velumanohar2000/IEEE-R5-Robotics-2024/Software/Testing/motor_calibration/src/main.cpp

#include <Arduino.h>
#include <stdbool.h>
#include <Adafruit_BNO08x.h>
#include <Wire.h>
#include <math.h>
#include <ESP32MotorControl.h>
#include <LiquidCrystal_I2C.h>
#include <string.h>

#include "BNO085_heading_acceleration.h"
#include "motor_control_v2.h"
//#include "printToLcd.h"

// #define CALIBRATE_STRAIGHT_LINE
//  #define TEST_TURNS

// After starting/resetting the robot you have 5 seconds to align it with 0 degress
// We need to implement a blovking function that waits unitl button pressed before locking in 0
// Also we need to implement a lcd screen to show us our angle without uart

/*
 * Global Variables for LCD Display
 */
LiquidCrystal_I2C lcd(0x27, 16, 2); // set the LCD address to 0x27 for a 16 chars and 2 line display
char lcdStr[16];
/*
 *Global Variable for the Motors
 */
ESP32MotorControl motors;
// LEFT MOTOR
const uint8_t MOTOR_A_IN_1 = 5;
const uint8_t MOTOR_A_IN_2 = 4;
int16_t A_LEFT_MOTOR_OFFSET = 0;

// RIGHT MOTOR
const uint8_t MOTOR_B_IN_3 = 7;
const uint8_t MOTOR_B_IN_4 = 6;
int16_t B_RIGHT_MOTOR_OFFSET = 2;

/*
 * Global Variable for IMU
 */
Adafruit_BNO08x bno08x;
sh2_SensorValue_t sensorValue;
float offset = 0;

// float getHeading()
// {

//   float retVal = -1;

//   if (bno08x.getSensorEvent(&sensorValue))
//   {
//     retVal = calculateHeading(sensorValue.un.arvrStabilizedRV.i, sensorValue.un.arvrStabilizedRV.j, sensorValue.un.arvrStabilizedRV.k, sensorValue.un.arvrStabilizedRV.real);

//     retVal -= offset;
//     if (retVal < 0)
//     {
//       retVal += 359.99;
//     }
//   }

//   return retVal;
// }
// float getCurrentAngle()
// {
//   float currentAngle = -1;
//   while (currentAngle == -1)
//   {
//     currentAngle = getHeading();
//   }
//   return currentAngle;
// }
// void printCurrentAngle()
// {
//   float currentAngle = getCurrentAngle();
//   printToLcd("Current Angle: ", currentAngle);
// }

// void turnToHeading(float goal, uint8_t speed)
// {
//   float absVal;
//   float angleDiff;
//   uint8_t i = 0;

//   float currentAngle = getCurrentAngle();

//   printToLcd("Current Angle: ", currentAngle);
//   angleDiff = goal - currentAngle;
//   absVal = abs(angleDiff);
//   if (absVal > 350)
//   {
//     absVal = 359.99 - absVal;
//     angleDiff = 359.99 - angleDiff;
//   }
//   Serial.println(angleDiff);
//   Serial.println(absVal);
//   Serial.println();

//   while (absVal > 10)
//   {
//     // Serial.print("abs: ");
//     // Serial.print(absVal);
//     // Serial.print(" angle: ");
//     // Serial.print(currentAngle);

//     if ((angleDiff >= 0) && (absVal <= 180))
//     {
//       // Serial.print(" case 1: ");
//       turn(COUNTER_CLOCKWISE, speed);
//     }
//     else if ((angleDiff < 0) && (absVal <= 180))
//     {
//       // Serial.print(" case 2: ");
//       turn(CLOCKWISE, speed);
//     }
//     else if ((angleDiff >= 0) && (absVal >= 180))
//     {
//       // Serial.print(" case 3: ");
//       turn(CLOCKWISE, speed);
//     }
//     else
//     {
//       // Serial.print(" case 4: ");
//       turn(COUNTER_CLOCKWISE, speed);
//     }

//     currentAngle = getCurrentAngle();
//     i++;
//     if (i >= 30)
//     {
//       printCurrentAngle();
//       i = 0;
//     }

//     // Serial.println(goal);
//     angleDiff = goal - currentAngle;
//     absVal = abs(angleDiff);
//     if (absVal > 350)
//     {
//       absVal = 359.99 - absVal;
//       angleDiff = 359.99 - angleDiff;
//     }
//     Serial.println(angleDiff);
//     Serial.println(absVal);
//     Serial.println();
//   }
//   stop();
// }

void testTurns()
{
  turnToHeading(90, 85);
  /// printCurrentAngle();
  delay(1000);

  turnToHeading(0, 85);
  // printCurrentAngle();
  delay(1000);

  turnToHeading(180, 85);
  // printCurrentAngle();
  delay(1000);

  turnToHeading(0, 85);
  // printCurrentAngle();
  delay(1000);

  turnToHeading(270, 85);
  // printCurrentAngle();
  delay(1000);

  turnToHeading(45, 85);
  // printCurrentAngle();
  delay(1000);

  turnToHeading(225, 85);
  // printCurrentAngle();
  delay(1000);

  turnToHeading(135, 85);
  // printCurrentAngle();
  delay(1000);

  turnToHeading(315, 85);
  // printCurrentAngle();
  delay(1000);
}

void setup()
{
  Serial.begin(115200);
  Wire.begin(9, 8);

  lcd.init(); // initialize the lcd
  lcd.backlight();

  setupBNO085(&bno08x);
  motors.attachMotors(MOTOR_A_IN_1, MOTOR_A_IN_2, MOTOR_B_IN_3, MOTOR_B_IN_4);
  float currentAngle;
  uint8_t i = 0;
  Serial.println("*****TEST HEADING******\n\n");

  // printToLcd("HEADING", "TEST");
  delay(1000);
  // printToLcd("Position to 0", "degrees");

  for (i = 3; i > 0; i--)
  {
    //   printToLcd("Time left: ", i);
    delay(1000);
  }

  offset = getCurrentAngle();

  Serial.println("offset: ");
  Serial.println(offset);

  currentAngle = getCurrentAngle();

  Serial.print("Current Angle: ");
  Serial.println(currentAngle);

 // printToLcd("OFFSET:", offset);
  delay(1000);
  // printCurrentAngle();
  delay(1000);
}
// void driveToHeading(float goalHeading)
// {
//   float currentAngle = -1;
//   float absVal;
//   float angleDiff;
//   unsigned long currentMillis;
//   unsigned long previousMillis = 0;
//   uint32_t interval = 1000;
//   uint16_t i = 0;

//   bool goToHeading = true;
//   while (goToHeading)
//   {
//     currentAngle = getCurrentAngle();

//     i++;
//     if (i == 30)
//     {
//       printToLcd("Current Angle: ", currentAngle);
//       i = 0;
//     }
//     angleDiff = goalHeading - currentAngle;
//     absVal = abs(angleDiff);
//     // Serial.println(absVal);
//     if (absVal > 345)
//     {
//       absVal = 359.99 - absVal;
//       angleDiff = 359.99 - angleDiff;
//     }
//     Serial.println(angleDiff);
//     Serial.println(absVal);
//     Serial.println();

//     if (absVal > 15)
//     {
//       turnToHeading(goalHeading, 65);
//       previousMillis = currentMillis = millis();
//     }
//     else if (absVal <= 15 && absVal >= 3)
//     {
//       if ((angleDiff >= 0) && (absVal <= 180))
//       {
//         // Serial.print(" case 1: ");
//         turn2(COUNTER_CLOCKWISE, 65, 30);
//       }
//       else if ((angleDiff < 0) && (absVal <= 180))
//       {
//         // Serial.print(" case 2: ");
//         turn2(CLOCKWISE, 65, 30);
//       }
//       else if ((angleDiff >= 0) && (absVal >= 180))
//       {
//         // Serial.print(" case 3: ");
//         turn2(CLOCKWISE, 65, 30);
//       }
//       else
//       {
//         // Serial.print(" case 4: ");
//         turn2(COUNTER_CLOCKWISE, 65, 30);
//       }
//       previousMillis = currentMillis = millis();
//     }
//     else if (absVal < 5 && absVal >= 2)
//     {
//       if ((angleDiff >= 0) && (absVal <= 180))
//       {
//         // Serial.print(" case 1: ");
//         turn2(COUNTER_CLOCKWISE, 65, 10);
//       }
//       else if ((angleDiff < 0) && (absVal <= 180))
//       {
//         // Serial.print(" case 2: ");
//         turn2(CLOCKWISE, 65, 10);
//       }
//       else if ((angleDiff >= 0) && (absVal >= 180))
//       {
//         // Serial.print(" case 3: ");
//         turn2(CLOCKWISE, 65, 10);
//       }
//       else
//       {
//         // Serial.print(" case 4: ");
//         turn2(COUNTER_CLOCKWISE, 65, 10);
//       }
//       unsigned long currentMillis = millis();

//       if (currentMillis - previousMillis >= interval)
//       {
//         previousMillis = currentMillis;
//         if (previousMillis != 0)
//         {
//           goToHeading = false;
//           stop();
//         }
//       }
//     }
//     else
//     {
//       move(FORWARD, 65);

//       if (currentMillis - previousMillis >= interval)
//       {
//         previousMillis = currentMillis;
//         if (previousMillis != 0)
//         {
//           goToHeading = false;
//           stop();
//         }
//       }
//     }
//   }
// }

void calibrateStraightLine()
{
  move(FORWARD, 75);
  delay(4000);
  stop();
  move(BACKWARD, 75);
  delay(4000);
  stop();
}

unsigned long currentMillis = 0;
unsigned long previousMillis = 0; // will store last time LED was updated

void loop()
{
#ifdef CALIBRATE_STRAIGHT_LINE
  calibrateStraightLine(); // change, left and right motor offset untill car goes straight for 4 seconds
  while (1)
    ;
#endif
#ifdef TEST_TURNS
  turn(COUNTER_CLOCKWISE);
  delay(2000);
  turn(CLOCKWISE);
  delay(2000);
  stop();
  delay(2000);
  testTurns(); // fix turning speed until angle is within desired range of goal heading
#endif
  previousMillis = currentMillis = millis();
  while (currentMillis - previousMillis < 1000)
  {
    driveToHeading(270);
    currentMillis = millis();
  }
  stop();
  delay(1000);
  previousMillis = currentMillis = millis();

  while (currentMillis - previousMillis < 1000)
  {
    driveToHeading(0);
    currentMillis = millis();
  }
  stop();
  delay(1000);
  previousMillis = currentMillis = millis();

  while (currentMillis - previousMillis < 1000)
  {
    driveToHeading(90);
    currentMillis = millis();
  }
  stop();
  delay(1000);
  previousMillis = currentMillis = millis();

  while (currentMillis - previousMillis < 1000)
  {
    driveToHeading(180);
    currentMillis = millis();
  }
  stop();
  delay(1000);
}
