velumanohar2000/IEEE-R5-Robotics-2024/Software/Testing/front_lidar_test_VL53L4CX/src/main.cpp

/**
 ******************************************************************************
 * @file    VL53L4CX_Sat_HelloWorld_Interrupt.ino
 * @author  SRA
 * @version V1.0.0
 * @date    16 March 2022
 * @brief   Arduino test application for the STMicrolectronics VL53L4CX
 *          proximity sensor satellite based on FlightSense.
 *          This application makes use of C++ classes obtained from the C
 *          components' drivers.
 ******************************************************************************
 * @attention
 *
 * <h2><center>&copy; COPYRIGHT(c) 2022 STMicroelectronics</center></h2>
 *
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
 ******************************************************************************
 */

//On some boards like the Arduino Uno the pin used by the sensor to raise interrupts (A2)
//can't be mapped as an interrupt pin. For this this reason this sketch will not work
//unless some additional cabling is done and the interrupt pin is changed.
/*
 * To use this sketch you need to connect the VL53L4CD satellite sensor directly to the Nucleo board with wires in this way:
 * pin 1 (GND) of the VL53L4CD satellite connected to GND of the Nucleo board
 * pin 2 (VDD) of the VL53L4CD satellite connected to 3V3 pin of the Nucleo board
 * pin 3 (SCL) of the VL53L4CD satellite connected to pin D15 (SCL) of the Nucleo board
 * pin 4 (SDA) of the VL53L4CD satellite connected to pin D14 (SDA) of the Nucleo board
 * pin 5 (GPIO1) of the VL53L4CD satellite connected to pin A2 of the Nucleo board
 * pin 6 (XSHUT) of the VL53L4CD satellite connected to pin A1 of the Nucleo board
 */
/* Includes ------------------------------------------------------------------*/
#include <Arduino.h>
#include <Wire.h>
#include <vl53l4cx_class.h>
#include <string.h>
#include <stdlib.h>
#include <stdio.h>
#include <stdint.h>
#include <assert.h>
#include <stdlib.h>

#define DEV_I2C Wire
#define SerialPort Serial

#ifndef LED_BUILTIN
  #define LED_BUILTIN 13
#endif
#define LedPin LED_BUILTIN

#define interruptPin A2

// Components.
VL53L4CX sensor_vl53l4cx_sat(&DEV_I2C, A1);

volatile int interruptCount = 0;

void measure()
{
  interruptCount = 1;
}

void setup()
{
  VL53L4CX_Error status;
  // Led.
  pinMode(LedPin, OUTPUT);
  pinMode(interruptPin, INPUT_PULLUP);
  attachInterrupt(interruptPin, measure, FALLING);

  // Initialize serial for output.
  SerialPort.begin(115200);
  SerialPort.println("Starting...");

  // Initialize I2C bus.
  DEV_I2C.begin(9,8);

  // Configure VL53L4CX satellite component.
  sensor_vl53l4cx_sat.begin();

  // Switch off VL53L4CX satellite component.
  sensor_vl53l4cx_sat.VL53L4CX_Off();

  // Initialize VL53L4CX satellite component.
  status = sensor_vl53l4cx_sat.InitSensor(0x12);
  if (status) {
    SerialPort.println("Init sensor_vl53l4cx_sat failed...");
  }

  sensor_vl53l4cx_sat.VL53L4CX_StartMeasurement();
}

void loop()
{
  VL53L4CX_MultiRangingData_t MultiRangingData;
  VL53L4CX_MultiRangingData_t *pMultiRangingData = &MultiRangingData;
  uint8_t NewDataReady = 0;
  int no_of_object_found = 0, j;
  char report[64];
  if (interruptCount) {
    int status;

    interruptCount = 0;
    // Led blinking.
    digitalWrite(LedPin, HIGH);

    status = sensor_vl53l4cx_sat.VL53L4CX_GetMeasurementDataReady(&NewDataReady);
    if ((!status) && (NewDataReady != 0)) {
      status = sensor_vl53l4cx_sat.VL53L4CX_GetMultiRangingData(pMultiRangingData);
      no_of_object_found = pMultiRangingData->NumberOfObjectsFound;
      snprintf(report, sizeof(report), "Count=%d, #Objs=%1d ", pMultiRangingData->StreamCount, no_of_object_found);
      SerialPort.print(report);
      for (j = 0; j < no_of_object_found; j++) {
        if (j != 0) {
          SerialPort.print("\r\n                   ");
        }
        SerialPort.print("status=");
        SerialPort.print(pMultiRangingData->RangeData[j].RangeStatus);
        SerialPort.print(", D=");
        SerialPort.print(pMultiRangingData->RangeData[j].RangeMilliMeter);
        SerialPort.print("mm");
        SerialPort.print(", Signal=");
        SerialPort.print((float)pMultiRangingData->RangeData[j].SignalRateRtnMegaCps / 65536.0);
        SerialPort.print(" Mcps, Ambient=");
        SerialPort.print((float)pMultiRangingData->RangeData[j].AmbientRateRtnMegaCps / 65536.0);
        SerialPort.print(" Mcps");
      }
      SerialPort.println("");
      if (status == 0) {
        status = sensor_vl53l4cx_sat.VL53L4CX_ClearInterruptAndStartMeasurement();
      }
    }

    digitalWrite(LedPin, LOW);
  }
}
