velumanohar2000/IEEE-R5-Robotics-2024/Software/Testing/VL53L5CX_test/src/main.cpp

/*
  Read an 8x8 array of distances from the VL53L5CX
  By: Nathan Seidle
  SparkFun Electronics
  Date: October 26, 2021
  License: MIT. See license file for more information but you can
  basically do whatever you want with this code.

  This example shows how to read all 64 distance readings at once.

  Feel like supporting our work? Buy a board from SparkFun!
  https://www.sparkfun.com/products/18642

*/
#include <Arduino.h>

#include <Wire.h>

#include <SparkFun_VL53L5CX_Library.h> //http://librarymanager/All#SparkFun_VL53L5CX

SparkFun_VL53L5CX myImager;
VL53L5CX_ResultsData measurementData; // Result data class structure, 1356 byes of RAM

int imageResolution = 0; //Used to pretty print output
int imageWidth = 0; //Used to pretty print output

int imageArray[16];

void setup()
{
  Serial.begin(115200);
  delay(1000);
  Serial.println("SparkFun VL53L5CX Imager Example");

  Wire.begin(9, 8); //This resets to 100kHz I2C
  Wire.setClock(1000000); //Sensor has max I2C freq of 1MHz 
  
  Serial.println("Initializing sensor board. This can take up to 10s. Please wait.");
  if (myImager.begin() == false)
  {
    Serial.println(F("Sensor not found - check your wiring. Freezing"));
    while (1) ;
  }
  
  myImager.setResolution(4*4); //Enable all 64 pads
  
  imageResolution = myImager.getResolution(); //Query sensor for current resolution - either 4x4 or 8x8
  imageWidth = sqrt(imageResolution); //Calculate printing width

  bool response = myImager.setRangingFrequency(60);
  if (response == true)
  {
    int frequency = myImager.getRangingFrequency();
    if (frequency > 0)
    {
      Serial.print("Ranging frequency set to ");
      Serial.print(frequency);
      Serial.println(" Hz.");
    }
    else
      Serial.println(F("Error recovering ranging frequency."));
  }
  else
  {
    Serial.println(F("Cannot set ranging frequency requested. Freezing..."));
    while (1) ;
  }

  myImager.startRanging();
}

void loop()
{
  //Poll sensor for new data
  if (myImager.isDataReady() == true)
  {
    if (myImager.getRangingData(&measurementData)) //Read distance data into array
    {
      //The ST library returns the data transposed from zone mapping shown in datasheet
      //Pretty-print data with increasing y, decreasing x to reflect reality
      for (int y = 0 ; y <= imageWidth * (imageWidth - 1) ; y += imageWidth)
      {
        for (int x = imageWidth - 1 ; x >= 0 ; x--)
        {
          imageArray[x + y] = measurementData.distance_mm[x + y];
        }
      }
    }

    // Find the minimum value in imageArray
    int minValue = imageArray[0]; // Assume the first element is the minimum

    for (int i = 1; i < 16; i++)
    {
      if (imageArray[i] < minValue)
      {
        minValue = imageArray[i]; // Update the minimum value
      }
    }

    // Print the minimum value
    Serial.print("Minimum value: ");
    Serial.println(minValue);
  }

  delay(5); //Small delay between polling
}
