velumanohar2000/IEEE-R5-Robotics-2024/Software/Testing/ESP-NOW_Kill_Switch_Receiver/src/main.cpp

/*
 * Bit Bangers ESP-NOW "Kill Switch" Receiver Test Program
 * github.com/Bit-Bangers-UTA/Senior-Design
 * 
 * Authors:
 * Rolando Rosales
*/

// Libraries ------------------------------------------------------------------

#include <Kill_SW_RX.h>

// Defines --------------------------------------------------------------------

// Variables & Constants ------------------------------------------------------

// Structures & Classes -------------------------------------------------------

// Functions ------------------------------------------------------------------

void setup() {
  // Starts the kill switch RX demo
  initKillRX();
}
 
void loop() {

}
